leanderseige/solderfan/docs/photo-esp32fans-1.jpg

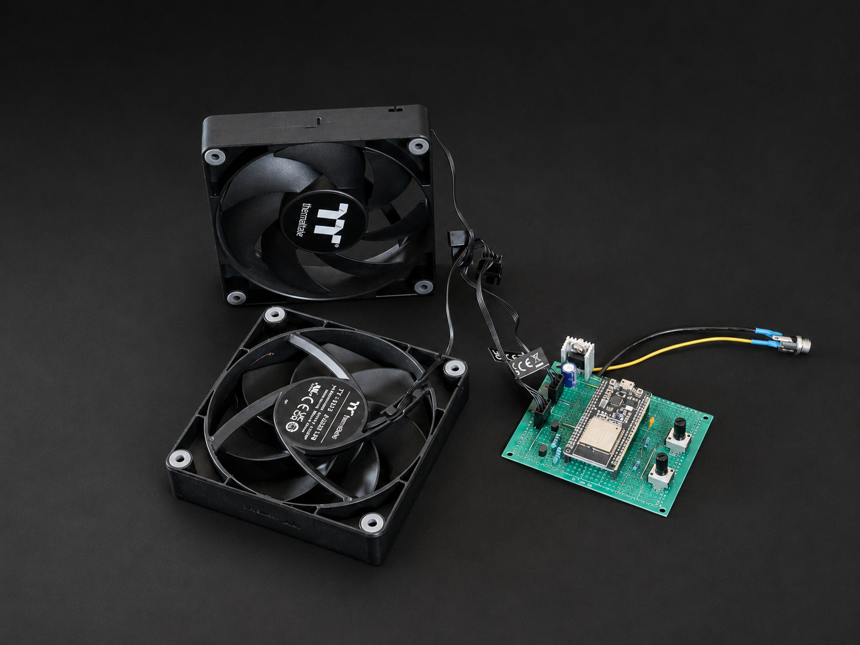
docs/photo-esp32fans-1.jpg
