leanderseige/solderfan/docs/photo-thickfilter-1.jpg

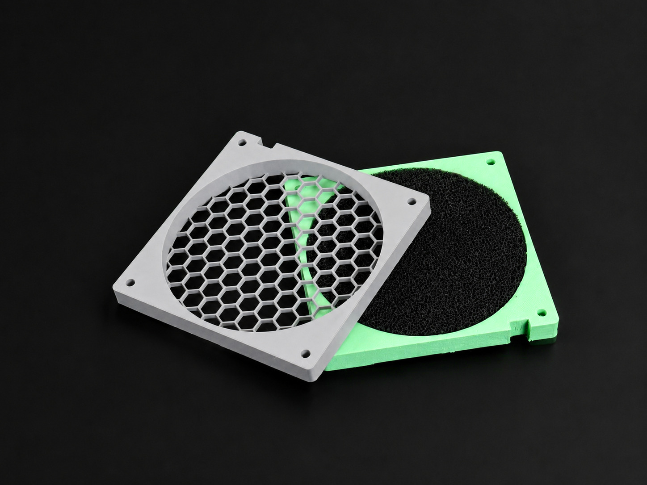
docs/photo-thickfilter-1.jpg
